MarcFinns/RDS-STEREO-HW-ENCODER/PICTURES/Front panel.jpeg

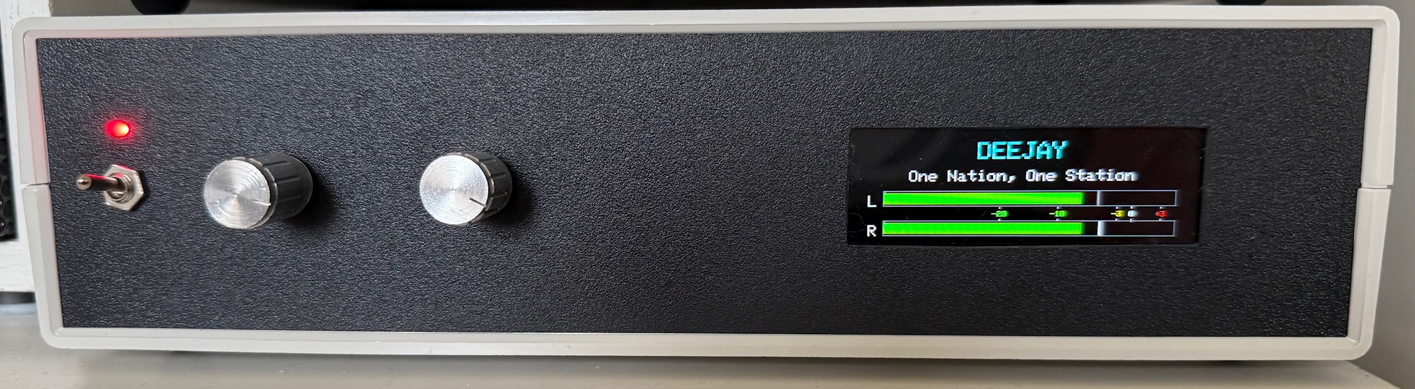
PICTURES/Front panel.jpeg
